p123ad/RummyKnockingMachine/doc/pics/01.jpg

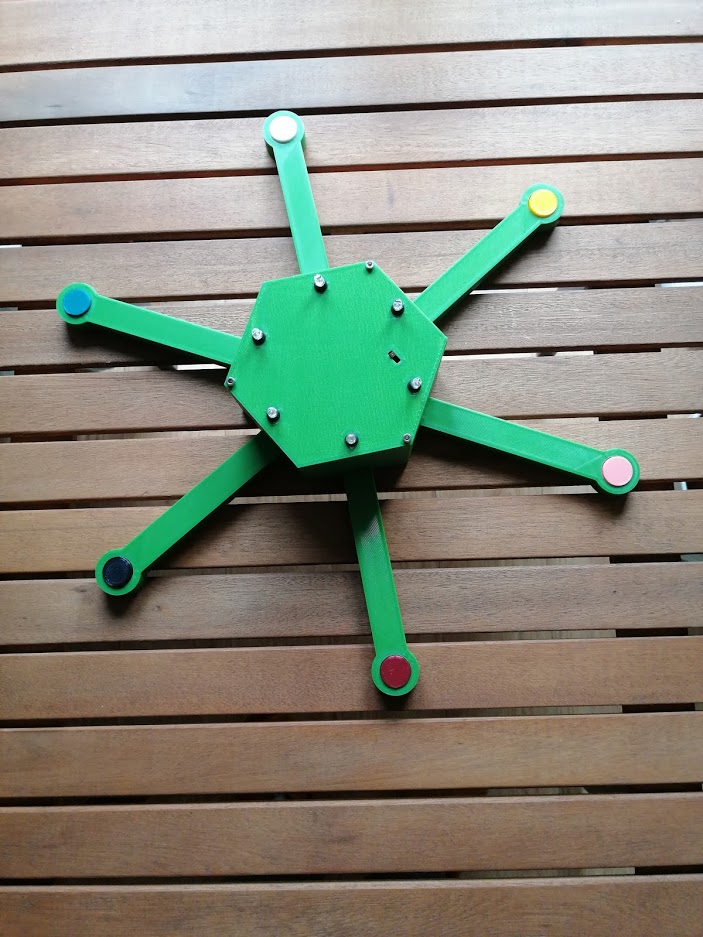
doc/pics/01.jpg
