p123ad/RummyKnockingMachine/doc/pics/02.jpg

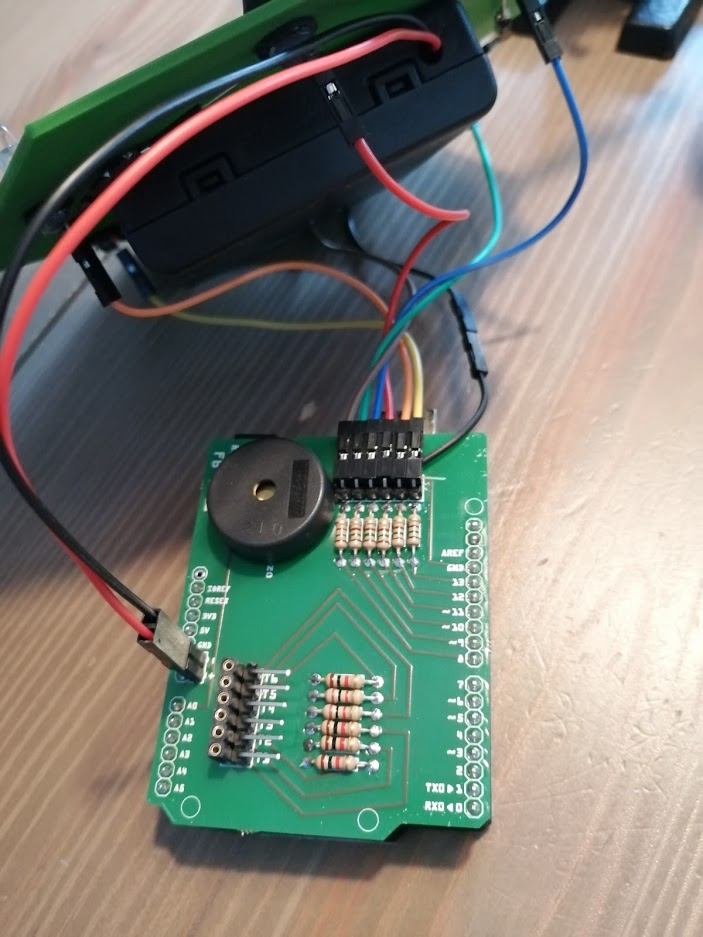
doc/pics/02.jpg
