p123ad/RummyKnockingMachine/doc/pics/03.jpg

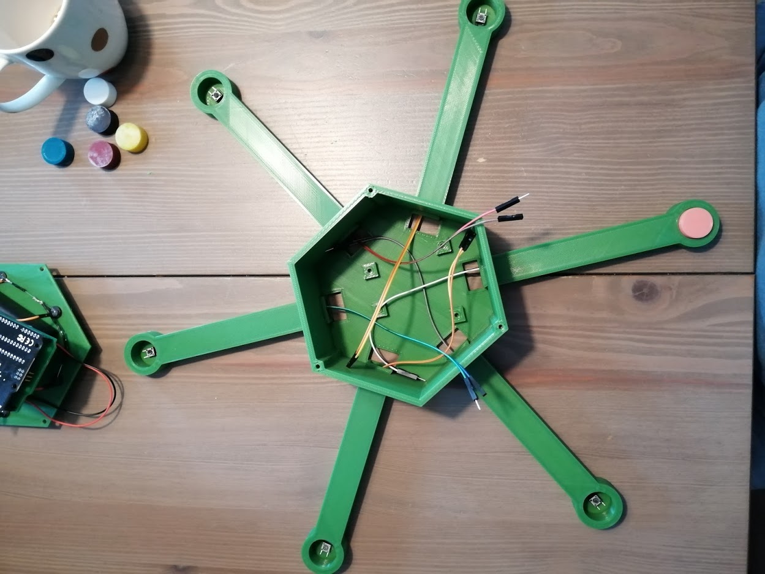
doc/pics/03.jpg
