p123ad/RummyKnockingMachine/doc/pics/04.jpg

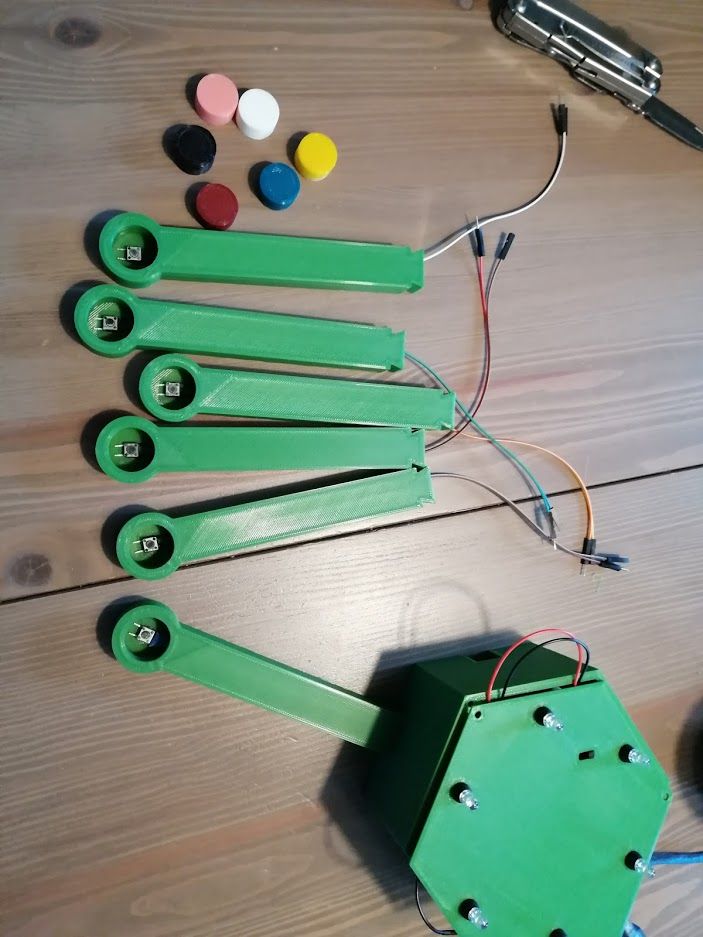
doc/pics/04.jpg
