p123ad/RummyKnockingMachine/doc/pics/05.jpg

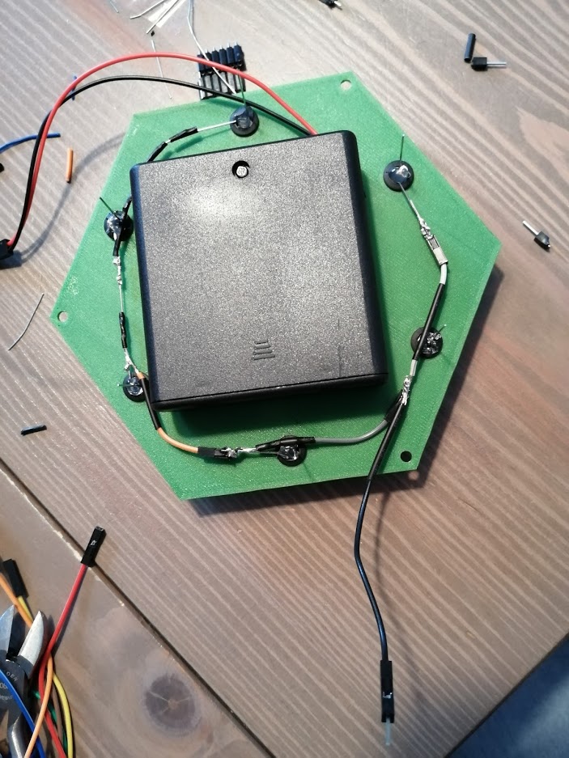
doc/pics/05.jpg
