p123ad/RummyKnockingMachine/doc/pics/06.jpg

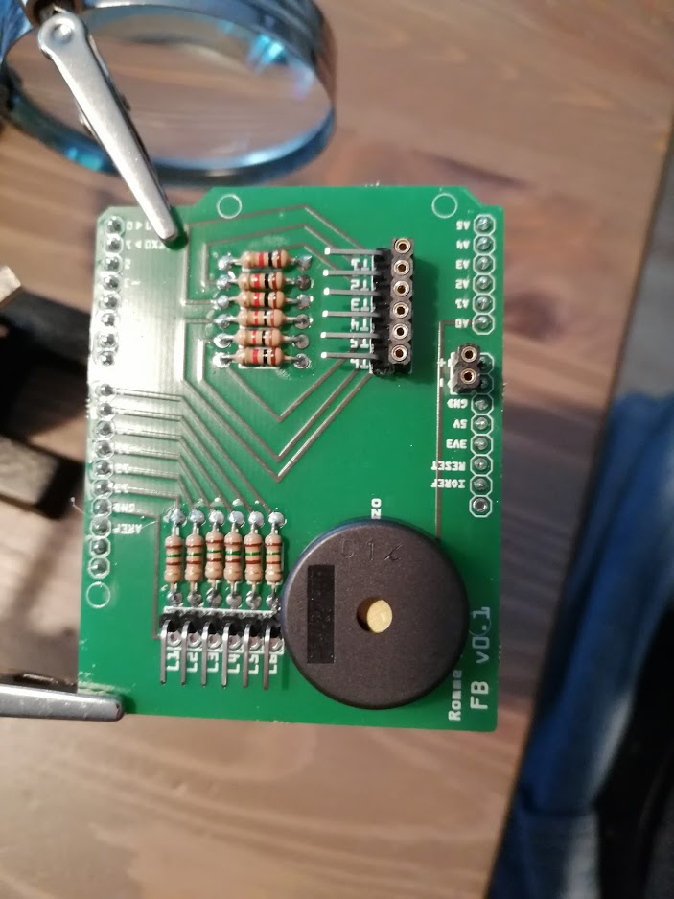
doc/pics/06.jpg
