p123ad/RummyKnockingMachine/doc/pics/07.jpg

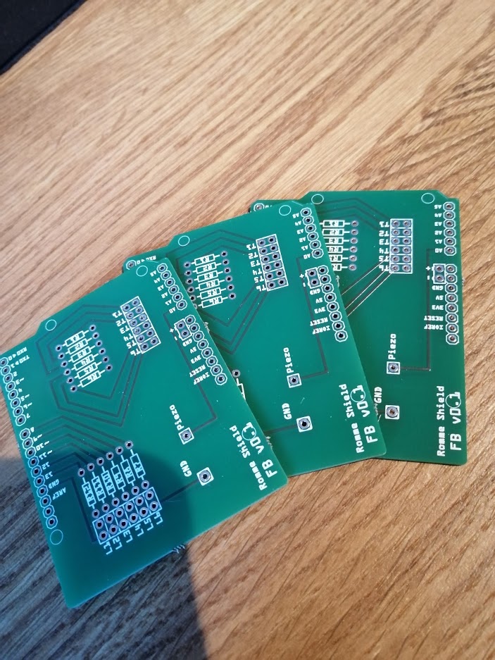
doc/pics/07.jpg
